djvs/hhkb/IMG_20210819_163000.jpg

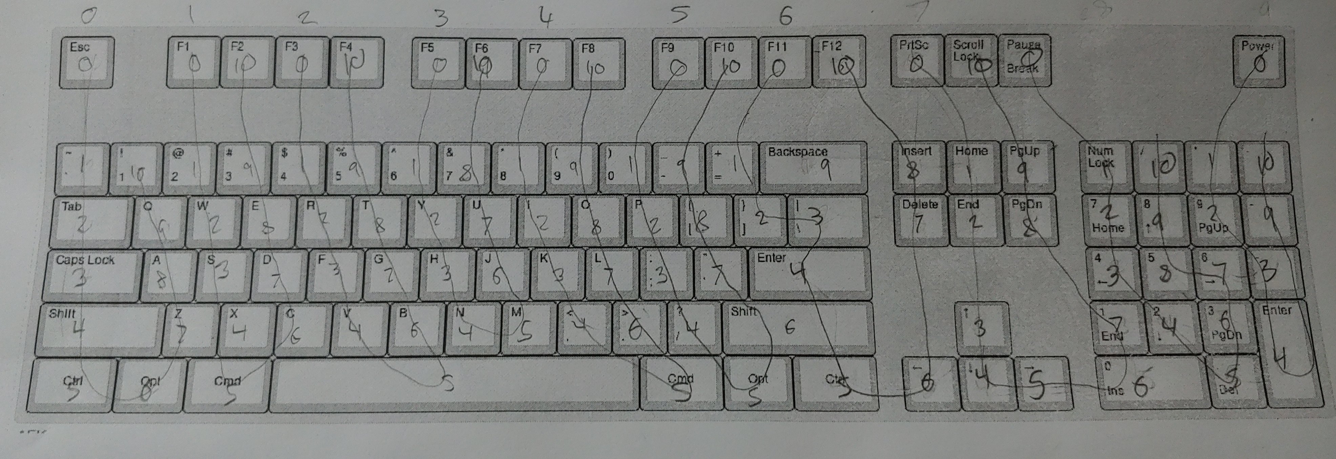
IMG_20210819_163000.jpg
